paullouisageneau/telebot/telebot-server/client/telebot.png

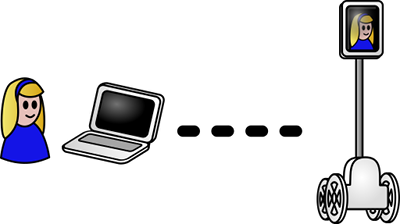
telebot-server/client/telebot.png
